uspat1234-bit/moto-gymkhana-timer/esp32_sketch/crowpanel/main_platformIO/include/FSImpl.h

/*
 FSImpl.h - base file system interface
 Copyright (c) 2015 Ivan Grokhotkov. All rights reserved.
 This file is part of the esp8266 core for Arduino environment.

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
 You should have received a copy of the GNU Lesser General Public
 License along with this library; if not, write to the Free Software
 Foundation, Inc., 51 Franklin St, Fifth Floor, Boston, MA  02110-1301  USA
 */
#ifndef FSIMPL_H
#define FSIMPL_H

#include <stddef.h>
#include <stdint.h>
#include <freertos/FreeRTOS.h>
#include <freertos/semphr.h>

namespace fs {

// RAII lock guard for the per-filesystem recursive mutex.
class FSLockGuard {
public:
  explicit FSLockGuard(SemaphoreHandle_t mtx) : _mtx(mtx) {
    if (_mtx) {
      xSemaphoreTakeRecursive(_mtx, portMAX_DELAY);
    }
  }
  ~FSLockGuard() {
    if (_mtx) {
      xSemaphoreGiveRecursive(_mtx);
    }
  }
  FSLockGuard(const FSLockGuard &) = delete;
  FSLockGuard &operator=(const FSLockGuard &) = delete;

private:
  SemaphoreHandle_t _mtx;
};

class FileImpl {
public:
  virtual ~FileImpl() {}
  virtual size_t write(const uint8_t *buf, size_t size) = 0;
  virtual size_t read(uint8_t *buf, size_t size) = 0;
  virtual void flush() = 0;
  virtual bool seek(uint32_t pos, SeekMode mode) = 0;
  virtual size_t position() const = 0;
  virtual size_t size() const = 0;
  virtual bool setBufferSize(size_t size) = 0;
  virtual void close() = 0;
  virtual time_t getLastWrite() = 0;
  virtual const char *path() const = 0;
  virtual const char *name() const = 0;
  virtual boolean isDirectory(void) = 0;
  virtual FileImplPtr openNextFile(const char *mode) = 0;
  virtual boolean seekDir(long position) = 0;
  virtual String getNextFileName(void) = 0;
  virtual String getNextFileName(bool *isDir) = 0;
  virtual void rewindDirectory(void) = 0;
  virtual operator bool() = 0;
};

class FSImpl {
protected:
  const char *_mountpoint;
  SemaphoreHandle_t _mtx;

public:
  FSImpl() : _mountpoint(NULL), _mtx(NULL) {}
  virtual ~FSImpl() {
    if (_mtx) {
      vSemaphoreDelete(_mtx);
    }
  }

  virtual FileImplPtr open(const char *path, const char *mode, const bool create) = 0;
  virtual bool exists(const char *path) = 0;
  virtual bool rename(const char *pathFrom, const char *pathTo) = 0;
  virtual bool remove(const char *path) = 0;
  virtual bool mkdir(const char *path) = 0;
  virtual bool rmdir(const char *path) = 0;
  void mountpoint(const char *);
  const char *mountpoint();
};

}  // namespace fs

#endif  //FSIMPL_H
